svofski/ledfilament/ltspice/pmos-boost.asc

C1: cap; 4.7e-6
D1: diode
L1: ind; 22e-3; Rser=10
M2: nmos; IRLML0040
R2: res; 100K
V1: voltage; 9; Rser=1
V2: voltage; PULSE(0 5 0 0 0 20e-5 30e-5)
Named nets: 0
.tran 0.05
